stephaniebarrett/printable-pc-case/v2/fan.scad

include <global.scad>


draw_fan_mounting_holes_offset(120,20);

// TODO: support other fan sizes and depths
function get_fan_spacing(size) =
    (size == 140) ?
        125 :
    (size == 120) ?
        105 :
    (size == 92) ?
        82.5 :
    (size == 80) ?
        71.5 :
    (size == 70) ?
        60 :
    (size == 60) ?
        50 :
    (size == 50) ?
        40 :
    (size == 40) ?
        32 :
    0;
             

module draw_fan(diameter, size, depth)
{
    difference()
    {
        cube([size, depth, size]);
        draw_fan_mounting_holes(size, depth);
        draw_fan_through_hole(diameter, size, depth);
    }
}

module draw_fan_mounting_holes(size, depth)
{
    spacing = get_fan_spacing(size);
    offset = (size-spacing)/2;
    
    for(x = [offset, offset+spacing])
    {
        for(z = [offset, offset+spacing])
        {
            translate([x, (depth+2)/2-1, z]) rotate([90,0,0]) cylinder(h=depth+2,d=FAN_MOUNTING_HOLE_DIAMETER,center=true, $fn=32);
        }
    }
}

module draw_fan_mounting_holes_offset(size, depth, radius)
{
    spacing = get_fan_spacing(size);
    offset = (size-spacing)/2;
    
    for(x = [offset, offset+spacing])
    {
        for(z = [offset, offset+spacing])
        {
            translate([x, depth, z]) rotate([90,0,0])  difference(){linear_extrude(depth) offset(r=radius){circle(d=FAN_MOUNTING_HOLE_DIAMETER, $fn=32);} translate([0,0,-0.5])linear_extrude(depth+1) circle(d=FAN_MOUNTING_HOLE_DIAMETER, $fn=32);}
        }
    }
}

module draw_fan_through_hole(diameter, size, depth)
{
    translate([size/2,(depth+2)/2-1,size/2]) rotate([90,0,0]) cylinder(h=depth+2,d=diameter,center=true, $fn=32);
}
